BenjiHansell/Radio-Controller/firmware/src/num_to_str.cpp

#include "num_to_str.hpp"

char unit_to_char(uint8_t unit){
  switch(unit){
    case 0: return '0'; break;
    case 1: return '1'; break;
    case 2: return '2'; break;
    case 3: return '3'; break;
    case 4: return '4'; break;
    case 5: return '5'; break;
    case 6: return '6'; break;
    case 7: return '7'; break;
    case 8: return '8'; break;
    case 9: return '9'; break;
    default: return '#'; break;
  }
  return '#';
}
